danmover/boarddock/docs/images/plates.png

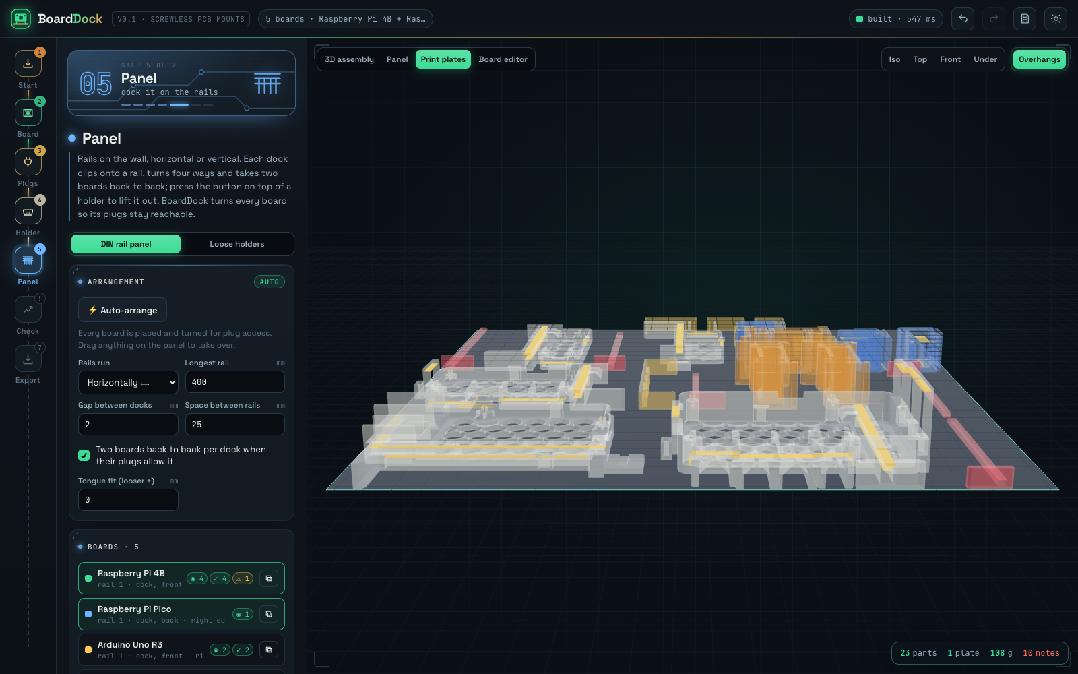
docs/images/plates.png
