danmover/boarddock/public/tiles/blank.webp

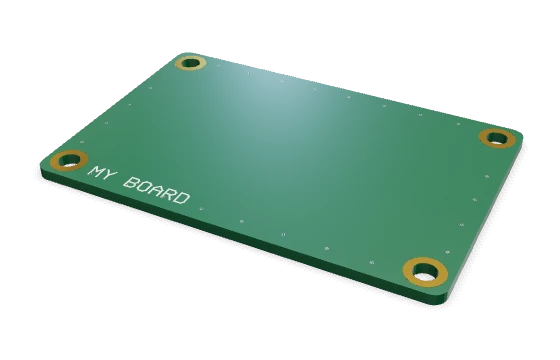
public/tiles/blank.webp
