danmover/boarddock/public/tiles/dc_pack_12v.webp

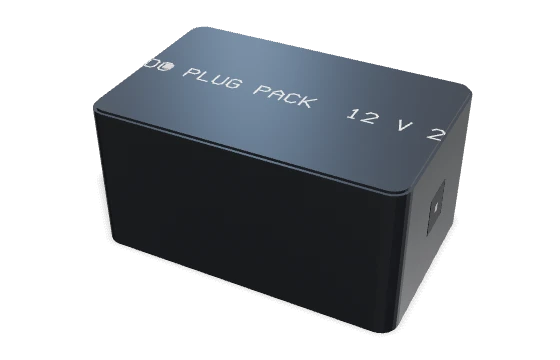
public/tiles/dc_pack_12v.webp
