danmover/boarddock/public/tiles/esp32.webp

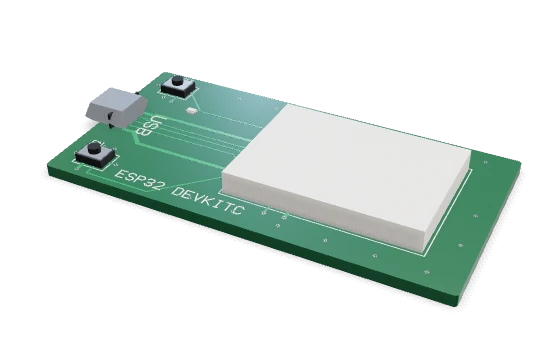
public/tiles/esp32.webp
