danmover/boarddock/public/tiles/example_dual_swd.webp

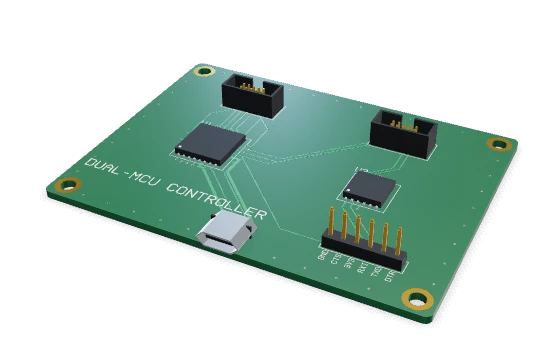
public/tiles/example_dual_swd.webp
