danmover/boarddock/public/tiles/example_jtag.webp

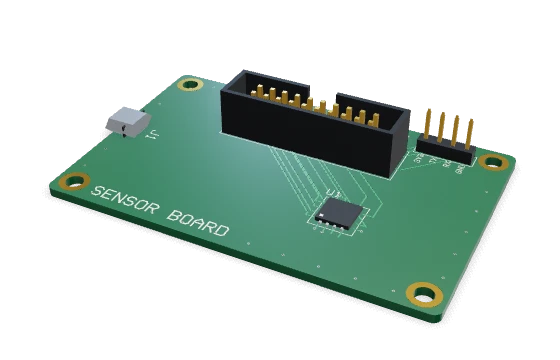
public/tiles/example_jtag.webp
