danmover/boarddock/public/tiles/ftdi.webp

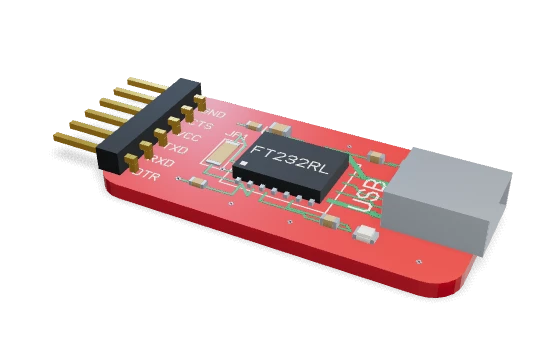
public/tiles/ftdi.webp
