danmover/boarddock/public/tiles/jlink.webp

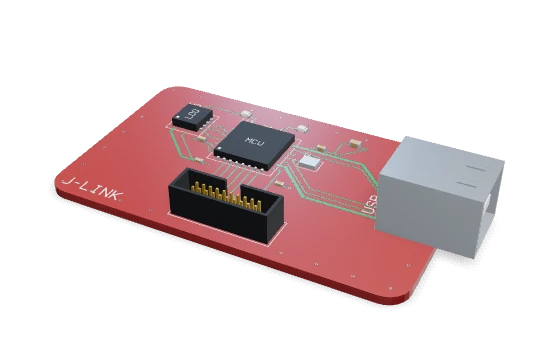
public/tiles/jlink.webp
