danmover/boarddock/public/tiles/mega.webp

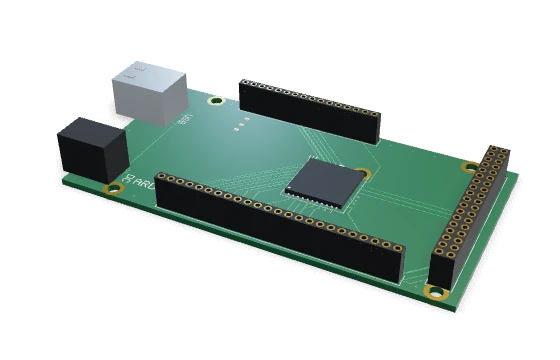
public/tiles/mega.webp
