danmover/boarddock/public/tiles/nano.webp

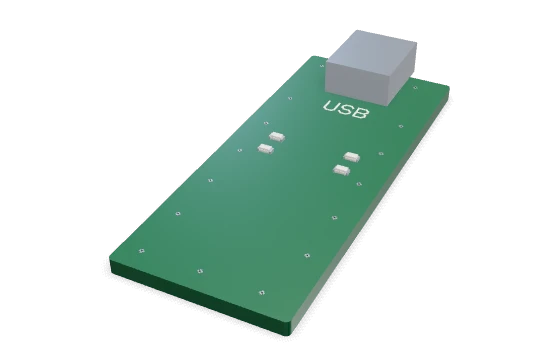
public/tiles/nano.webp
