danmover/boarddock/public/tiles/net_switch5.webp

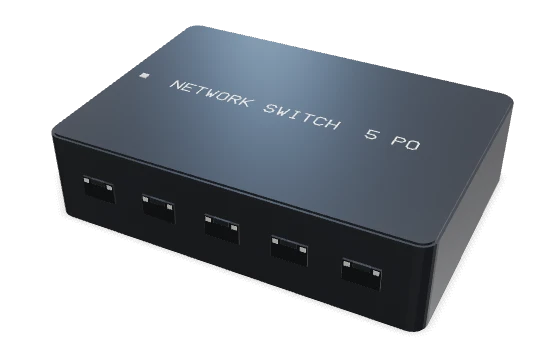
public/tiles/net_switch5.webp
