danmover/boarddock/public/tiles/net_switch8poe.webp

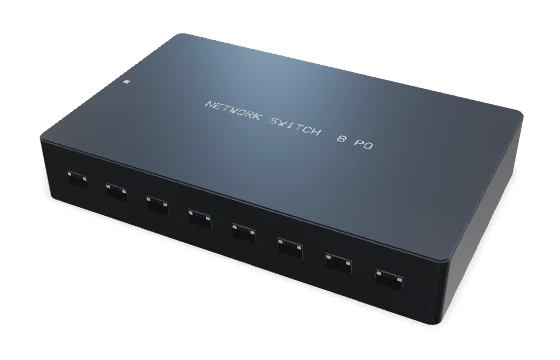
public/tiles/net_switch8poe.webp
