danmover/boarddock/public/tiles/pal/antenna.webp

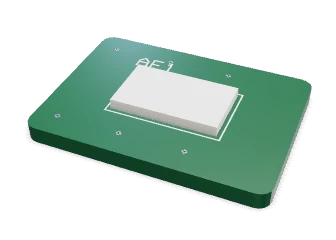
public/tiles/pal/antenna.webp
