danmover/boarddock/public/tiles/pal/b2b.webp

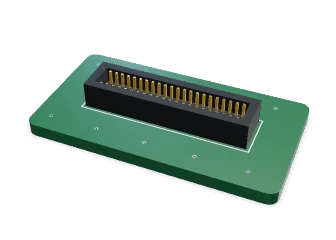
public/tiles/pal/b2b.webp
