danmover/boarddock/public/tiles/pal/button.webp

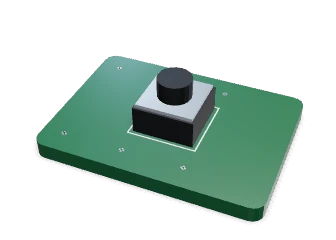
public/tiles/pal/button.webp
