danmover/boarddock/public/tiles/pal/buzzer.webp

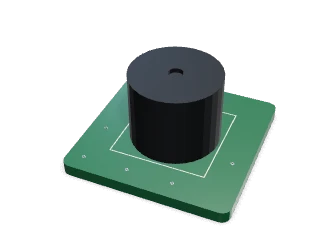
public/tiles/pal/buzzer.webp
