danmover/boarddock/public/tiles/pal/cap6.webp

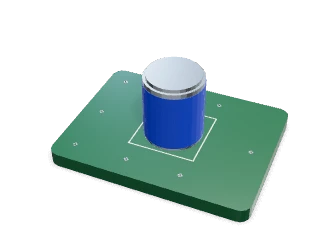
public/tiles/pal/cap6.webp
