danmover/boarddock/public/tiles/pal/coin.webp

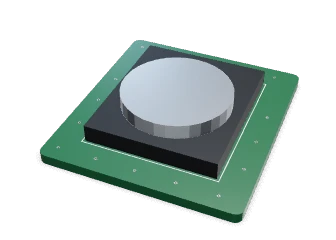
public/tiles/pal/coin.webp
