danmover/boarddock/public/tiles/pal/dbg_cortex20.webp

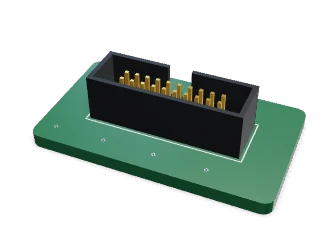
public/tiles/pal/dbg_cortex20.webp
