danmover/boarddock/public/tiles/pal/dbg_jtag20.webp

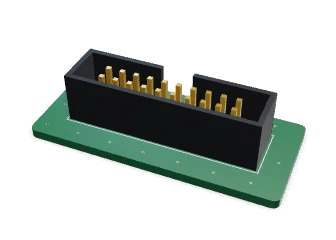
public/tiles/pal/dbg_jtag20.webp
