danmover/boarddock/public/tiles/pal/dbg_swd10.webp

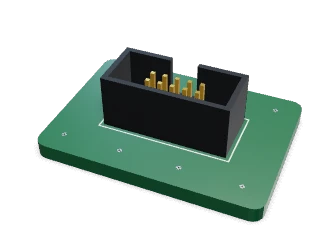
public/tiles/pal/dbg_swd10.webp
