danmover/boarddock/public/tiles/pal/dbg_tag.webp

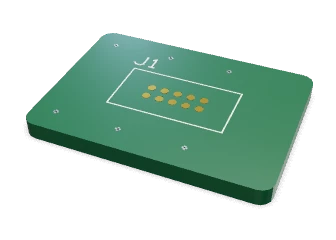
public/tiles/pal/dbg_tag.webp
