danmover/boarddock/public/tiles/pal/edge_audio35.webp

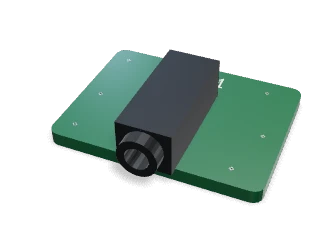
public/tiles/pal/edge_audio35.webp
