danmover/boarddock/public/tiles/pal/edge_banana.webp

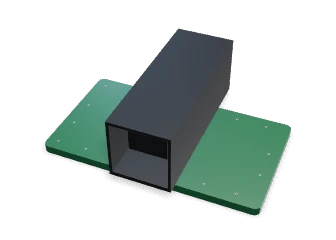
public/tiles/pal/edge_banana.webp
