danmover/boarddock/public/tiles/pal/edge_barrel.webp

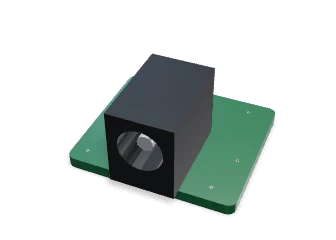
public/tiles/pal/edge_barrel.webp
