danmover/boarddock/public/tiles/pal/edge_bnc.webp

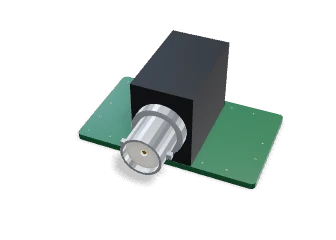
public/tiles/pal/edge_bnc.webp
