danmover/boarddock/public/tiles/pal/edge_custom.webp

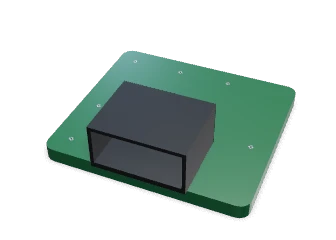
public/tiles/pal/edge_custom.webp
