danmover/boarddock/public/tiles/pal/edge_dp.webp

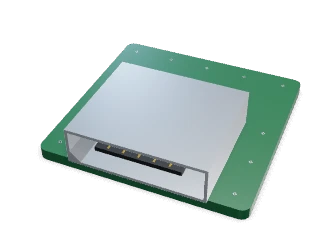
public/tiles/pal/edge_dp.webp
