danmover/boarddock/public/tiles/pal/edge_dsub.webp

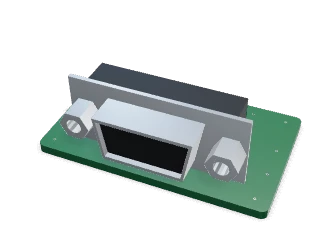
public/tiles/pal/edge_dsub.webp
