danmover/boarddock/public/tiles/pal/edge_fpc.webp

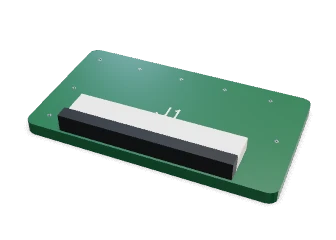
public/tiles/pal/edge_fpc.webp
