danmover/boarddock/public/tiles/pal/edge_hdmi_a.webp

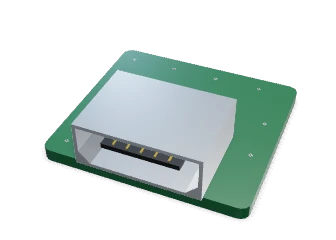
public/tiles/pal/edge_hdmi_a.webp
