danmover/boarddock/public/tiles/pal/edge_hdmi_micro.webp

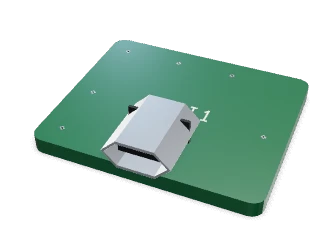
public/tiles/pal/edge_hdmi_micro.webp
