danmover/boarddock/public/tiles/pal/edge_idc_ra.webp

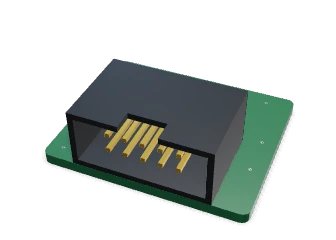
public/tiles/pal/edge_idc_ra.webp
