danmover/boarddock/public/tiles/pal/edge_iec_c7.webp

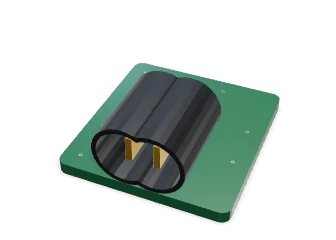
public/tiles/pal/edge_iec_c7.webp
