danmover/boarddock/public/tiles/pal/edge_iec_c14.webp

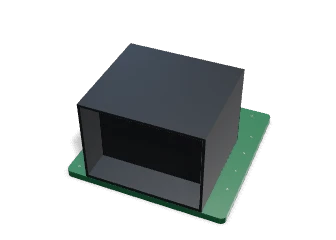
public/tiles/pal/edge_iec_c14.webp
