danmover/boarddock/public/tiles/pal/edge_m12.webp

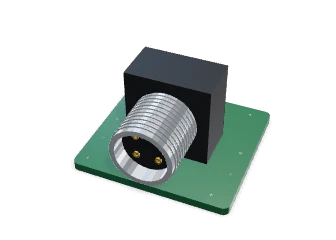
public/tiles/pal/edge_m12.webp
