danmover/boarddock/public/tiles/pal/edge_microsd.webp

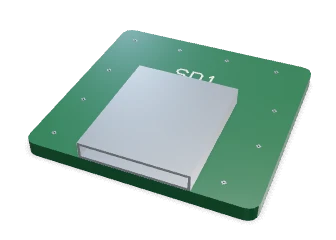
public/tiles/pal/edge_microsd.webp
