danmover/boarddock/public/tiles/pal/edge_minidin.webp

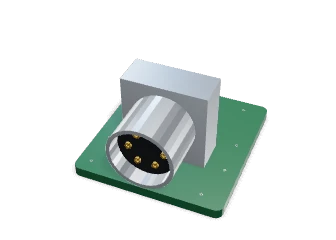
public/tiles/pal/edge_minidin.webp
