danmover/boarddock/public/tiles/pal/edge_pins_ra.webp

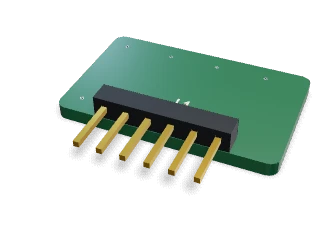
public/tiles/pal/edge_pins_ra.webp
