danmover/boarddock/public/tiles/pal/edge_qwiic.webp

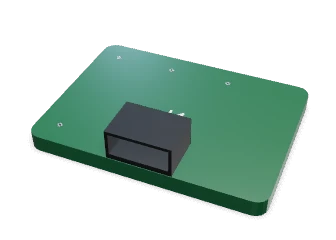
public/tiles/pal/edge_qwiic.webp
