danmover/boarddock/public/tiles/pal/edge_rca.webp

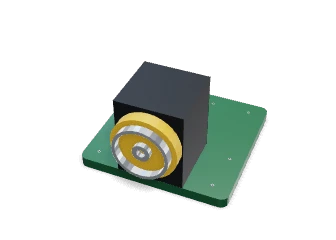
public/tiles/pal/edge_rca.webp
