danmover/boarddock/public/tiles/pal/edge_rf_mini.webp

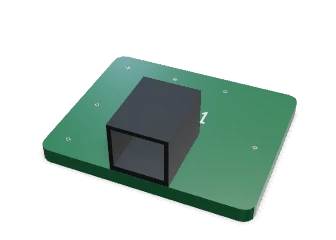
public/tiles/pal/edge_rf_mini.webp
