danmover/boarddock/public/tiles/pal/edge_rj11.webp

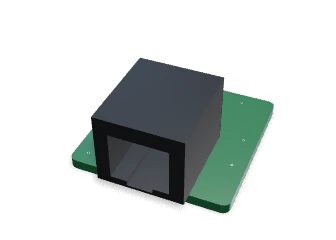
public/tiles/pal/edge_rj11.webp
