danmover/boarddock/public/tiles/pal/edge_rj45.webp

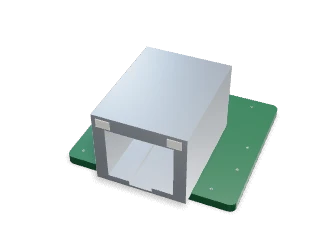
public/tiles/pal/edge_rj45.webp
