danmover/boarddock/public/tiles/pal/edge_sata.webp

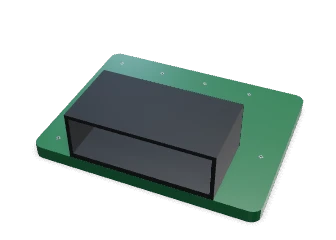
public/tiles/pal/edge_sata.webp
