danmover/boarddock/public/tiles/pal/edge_sd.webp

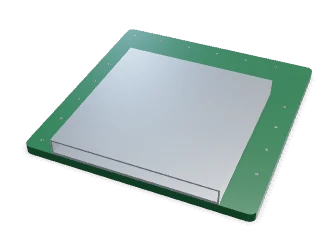
public/tiles/pal/edge_sd.webp
