danmover/boarddock/public/tiles/pal/edge_sfp.webp

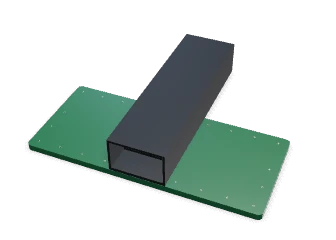
public/tiles/pal/edge_sfp.webp
