danmover/boarddock/public/tiles/pal/edge_sim.webp

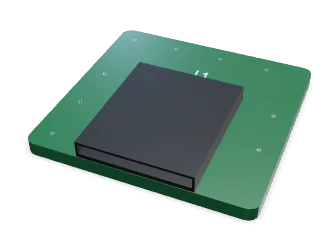
public/tiles/pal/edge_sim.webp
