danmover/boarddock/public/tiles/pal/edge_sma.webp

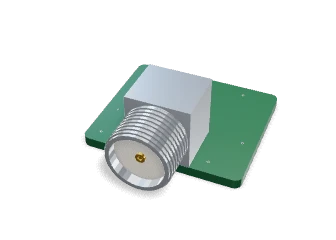
public/tiles/pal/edge_sma.webp
