danmover/boarddock/public/tiles/pal/edge_terminal.webp

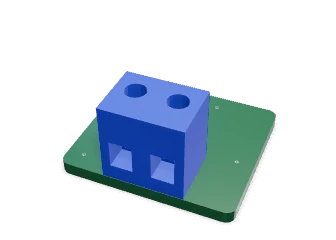
public/tiles/pal/edge_terminal.webp
