danmover/boarddock/public/tiles/pal/edge_usb_a.webp

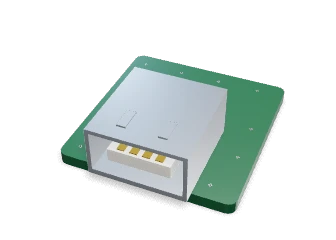
public/tiles/pal/edge_usb_a.webp
