danmover/boarddock/public/tiles/pal/edge_usb_a_dual.webp

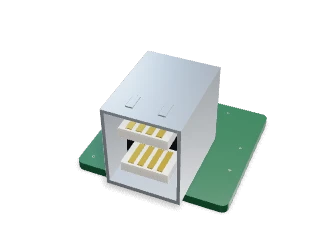
public/tiles/pal/edge_usb_a_dual.webp
