danmover/boarddock/public/tiles/pal/edge_usb_b.webp

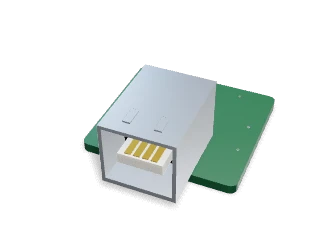
public/tiles/pal/edge_usb_b.webp
