danmover/boarddock/public/tiles/pal/edge_usb_mini_b.webp

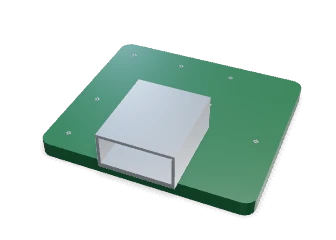
public/tiles/pal/edge_usb_mini_b.webp
