danmover/boarddock/public/tiles/pal/edge_wtb_side.webp

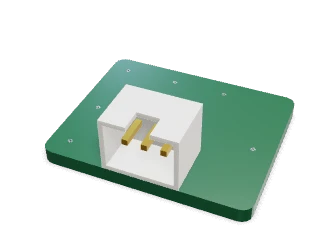
public/tiles/pal/edge_wtb_side.webp
