danmover/boarddock/public/tiles/pal/edge_xlr.webp

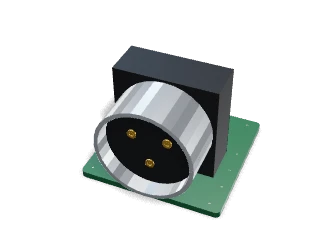
public/tiles/pal/edge_xlr.webp
