danmover/boarddock/public/tiles/pal/edge_xt30.webp

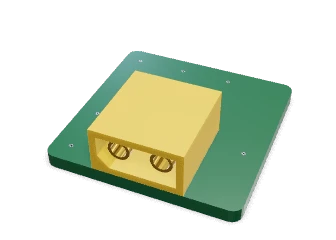
public/tiles/pal/edge_xt30.webp
