danmover/boarddock/public/tiles/pal/edge_xt60.webp

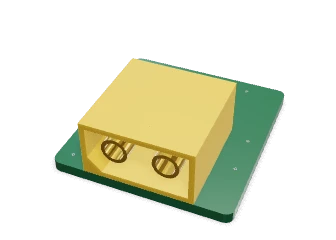
public/tiles/pal/edge_xt60.webp
