danmover/boarddock/public/tiles/pal/esp32.webp

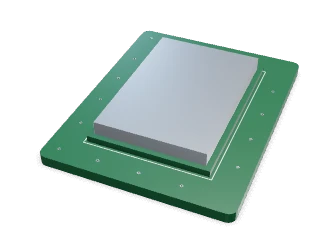
public/tiles/pal/esp32.webp
