danmover/boarddock/public/tiles/pal/fan4.webp

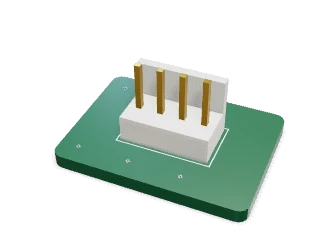
public/tiles/pal/fan4.webp
