danmover/boarddock/public/tiles/pal/gh4.webp

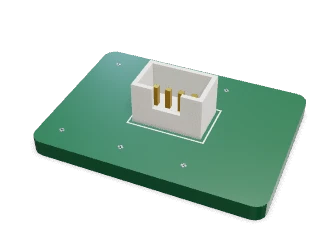
public/tiles/pal/gh4.webp
