danmover/boarddock/public/tiles/pal/hdr_1x8.webp

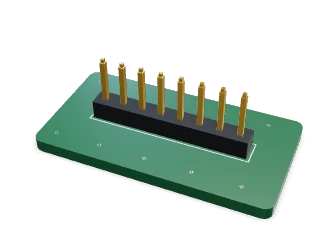
public/tiles/pal/hdr_1x8.webp
