danmover/boarddock/public/tiles/pal/hdr_2x10.webp

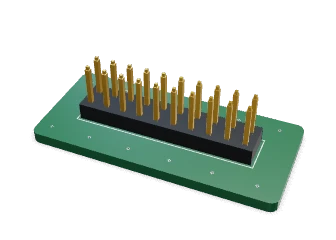
public/tiles/pal/hdr_2x10.webp
