danmover/boarddock/public/tiles/pal/hdr_2x20.webp

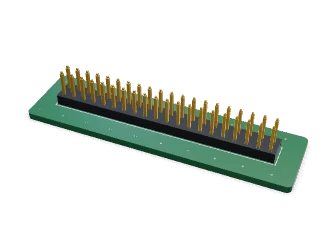
public/tiles/pal/hdr_2x20.webp
