danmover/boarddock/public/tiles/pal/heatsink.webp

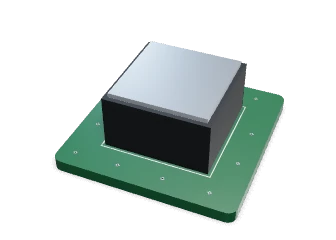
public/tiles/pal/heatsink.webp
