danmover/boarddock/public/tiles/pal/hole_M2.5.webp

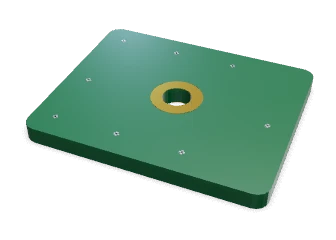
public/tiles/pal/hole_M2.5.webp
