danmover/boarddock/public/tiles/pal/idc10.webp

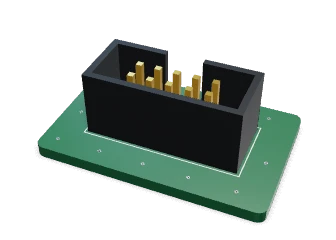
public/tiles/pal/idc10.webp
