danmover/boarddock/public/tiles/pal/idc16.webp

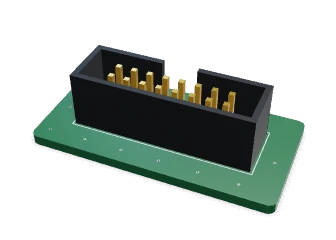
public/tiles/pal/idc16.webp
