danmover/boarddock/public/tiles/pal/jst_ph2.webp

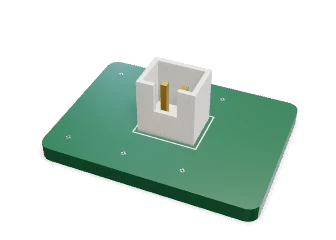
public/tiles/pal/jst_ph2.webp
