danmover/boarddock/public/tiles/pal/jst_ph3.webp

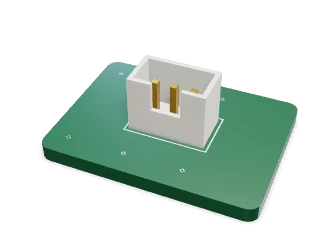
public/tiles/pal/jst_ph3.webp
