danmover/boarddock/public/tiles/pal/jst_xh2.webp

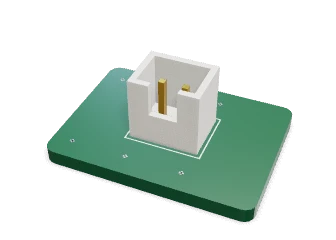
public/tiles/pal/jst_xh2.webp
