danmover/boarddock/public/tiles/pal/led5.webp

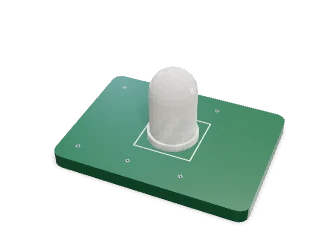
public/tiles/pal/led5.webp
