danmover/boarddock/public/tiles/pal/m2.webp

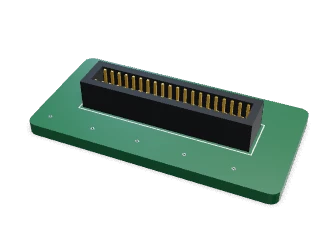
public/tiles/pal/m2.webp
