danmover/boarddock/public/tiles/pal/mfjr4.webp

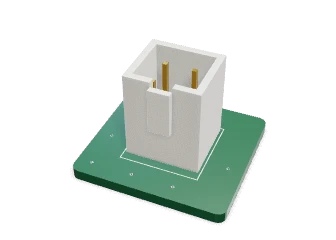
public/tiles/pal/mfjr4.webp
