danmover/boarddock/public/tiles/pal/pogo.webp

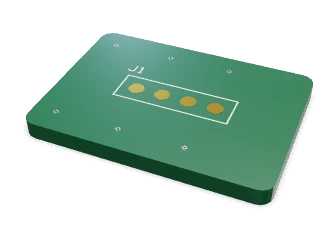
public/tiles/pal/pogo.webp
