danmover/boarddock/public/tiles/pal/pot.webp

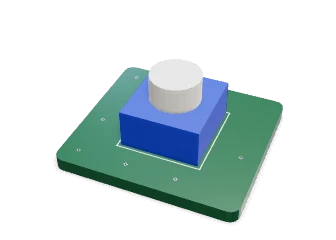
public/tiles/pal/pot.webp
