danmover/boarddock/public/tiles/pal/relay.webp

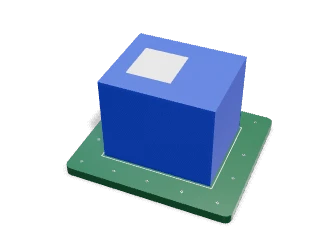
public/tiles/pal/relay.webp
