danmover/boarddock/public/tiles/pal/zh4.webp

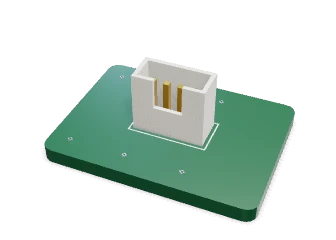
public/tiles/pal/zh4.webp
