danmover/boarddock/public/tiles/pb4.webp

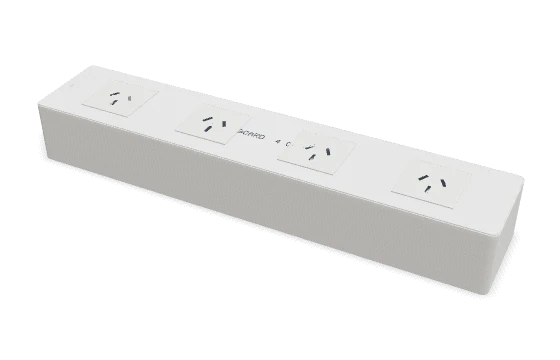
public/tiles/pb4.webp
