danmover/boarddock/public/tiles/pico.webp

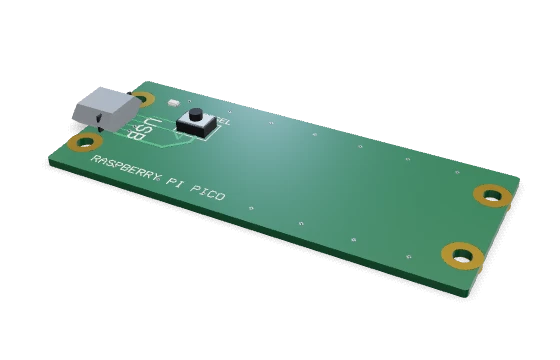
public/tiles/pico.webp
