danmover/boarddock/public/tiles/power_dist.webp

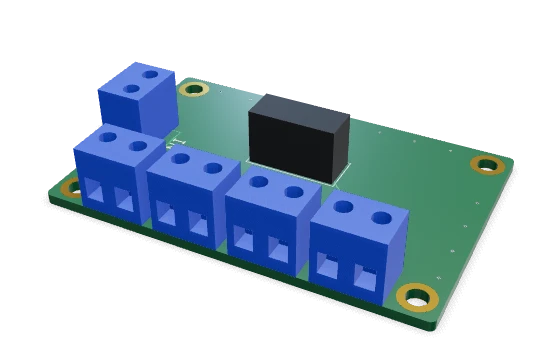
public/tiles/power_dist.webp
