danmover/boarddock/public/tiles/psu_pi4.webp

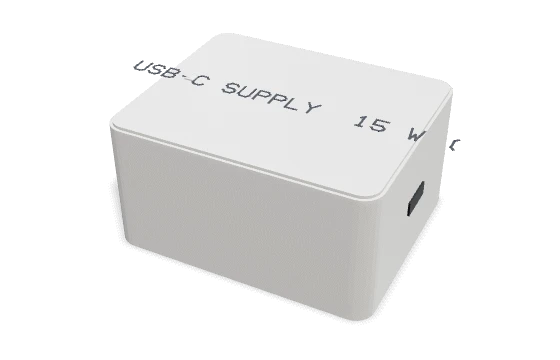
public/tiles/psu_pi4.webp
