danmover/boarddock/public/tiles/relay4.webp

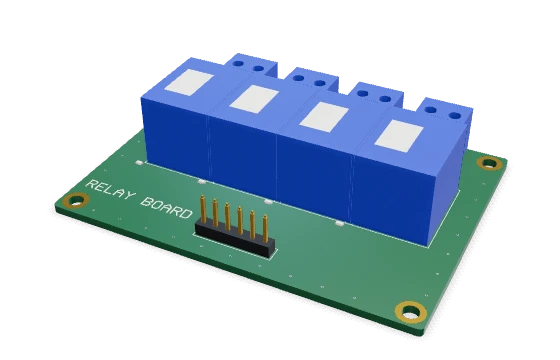
public/tiles/relay4.webp
