danmover/boarddock/public/tiles/rpi4.webp

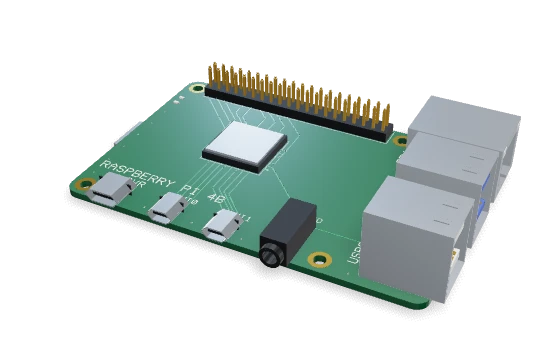
public/tiles/rpi4.webp
