danmover/boarddock/public/tiles/rpi_zero.webp

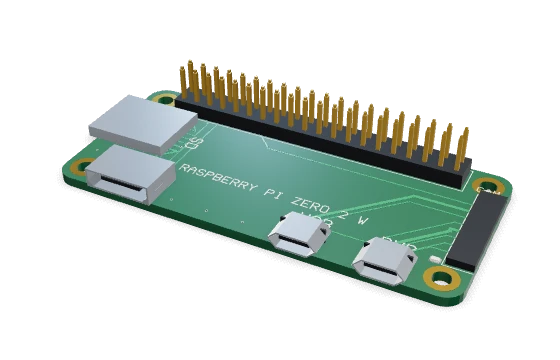
public/tiles/rpi_zero.webp
