danmover/boarddock/public/tiles/uno.webp

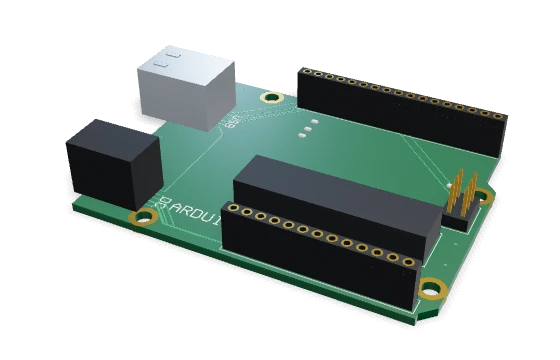
public/tiles/uno.webp
