danmover/boarddock/public/tiles/usb_charger6.webp

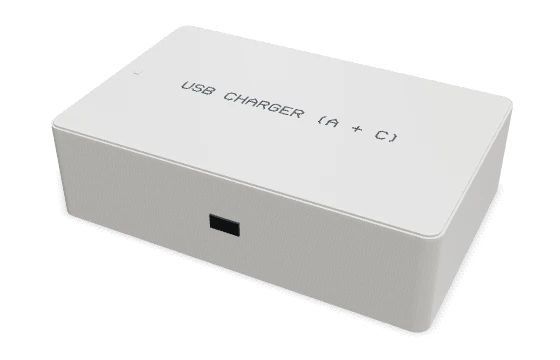
public/tiles/usb_charger6.webp
