danmover/boarddock/public/tiles/usb_charger.webp

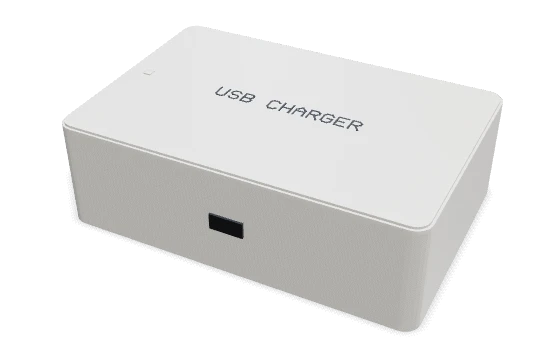
public/tiles/usb_charger.webp
