danmover/boarddock/public/tiles/usb_hub7.webp

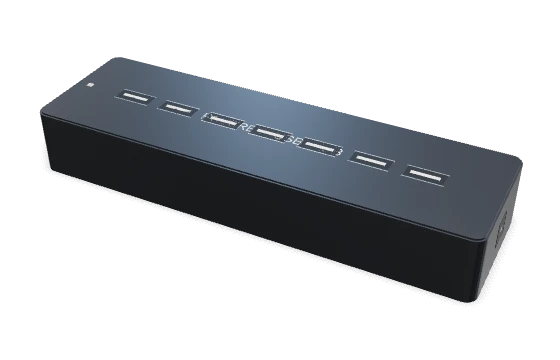
public/tiles/usb_hub7.webp
