danmover/boarddock/public/tiles/usb_hub.webp

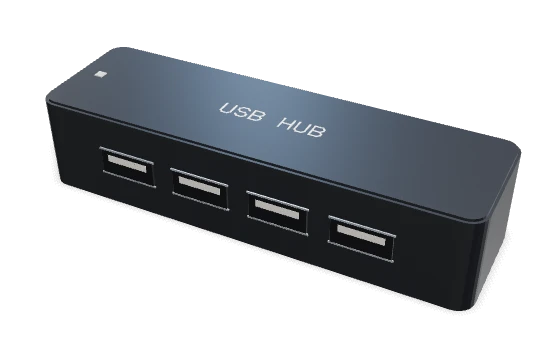
public/tiles/usb_hub.webp
